cphnano/spincoater/spinner_hardware/Parts/SOLW_20170704_coupling.SLDPRT

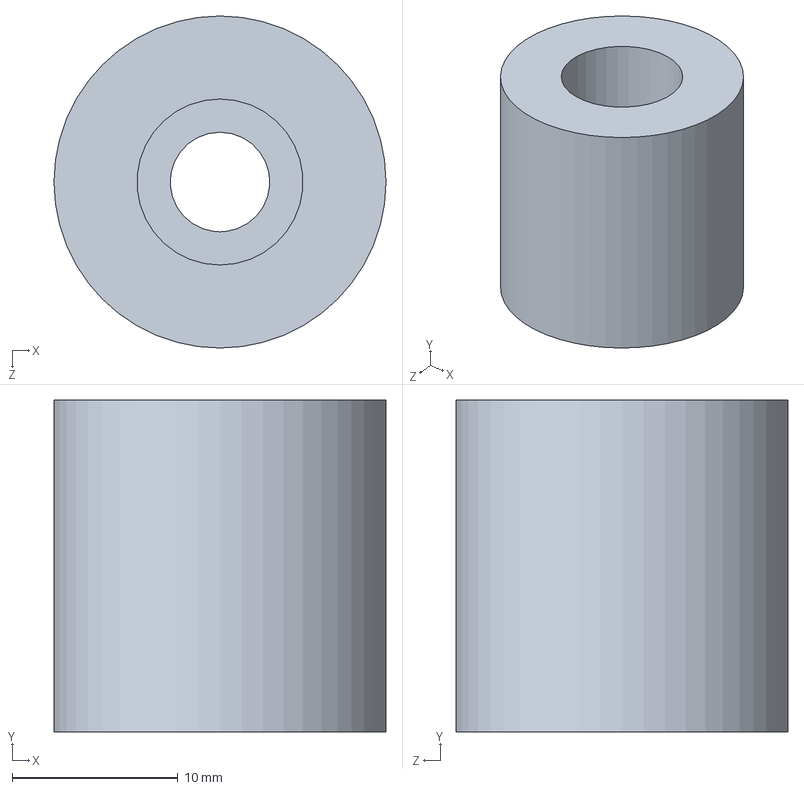
[picture p16: CAD file, 2019-01-21]
spinner_hardware/Parts/SOLW_20170704_coupling.SLDPRT
20.0 x 20.0 x 20.0 mm
