cphnano/spincoater/spinner_hardware/Parts/SOLW_20170703_Oring.SLDPRT

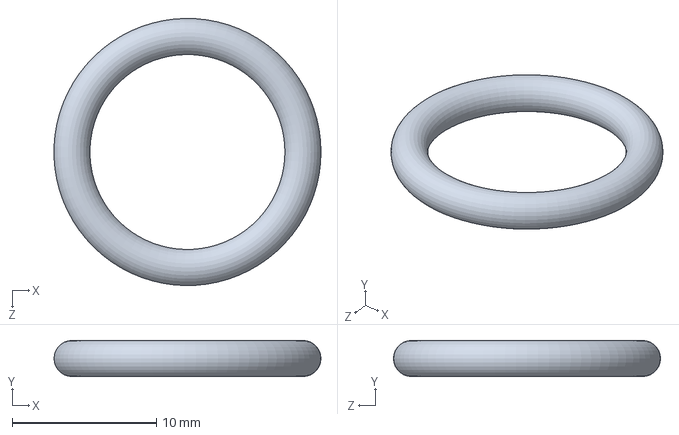
[picture p17: CAD file, 2019-01-21]
spinner_hardware/Parts/SOLW_20170703_Oring.SLDPRT
18.5 x 2.50 x 18.5 mm
