cphnano/spincoater/spinner_hardware/Parts/SOLW_20170707_JAw_Coupling_MJC25-10-A.SLDPRT

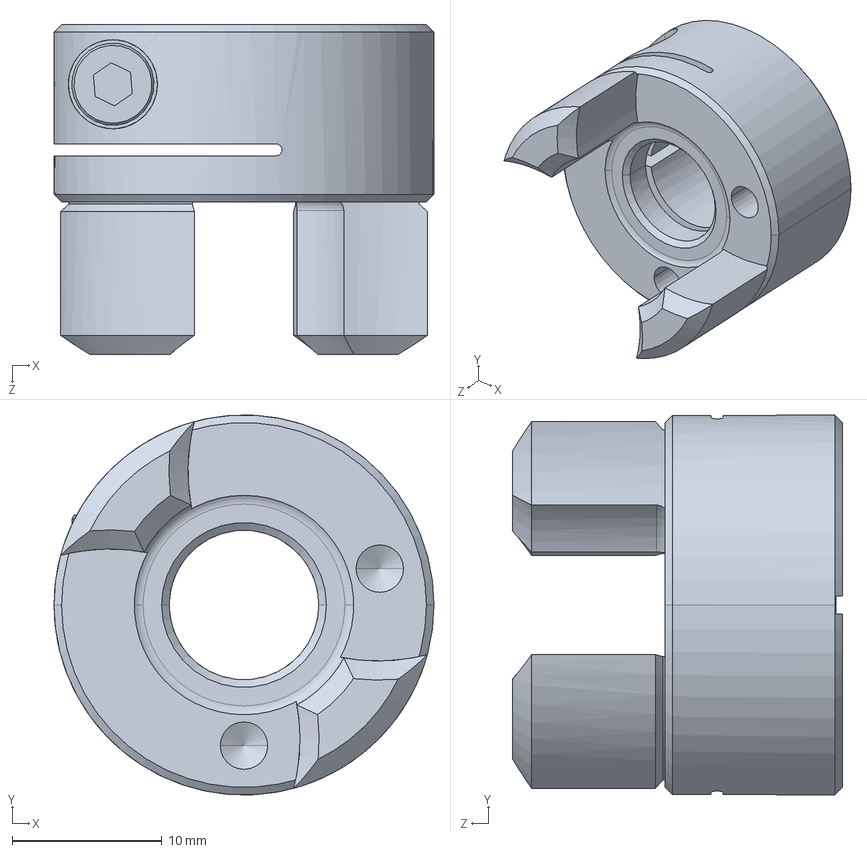
[picture p18: CAD file, 2019-01-21]
spinner_hardware/Parts/SOLW_20170707_JAw_Coupling_MJC25-10-A.SLDPRT
25.4 x 25.4 x 22.0 mm
