cphnano/spincoater/spinner_hardware/Parts/SOLW_20170703_static_clamp.SLDPRT

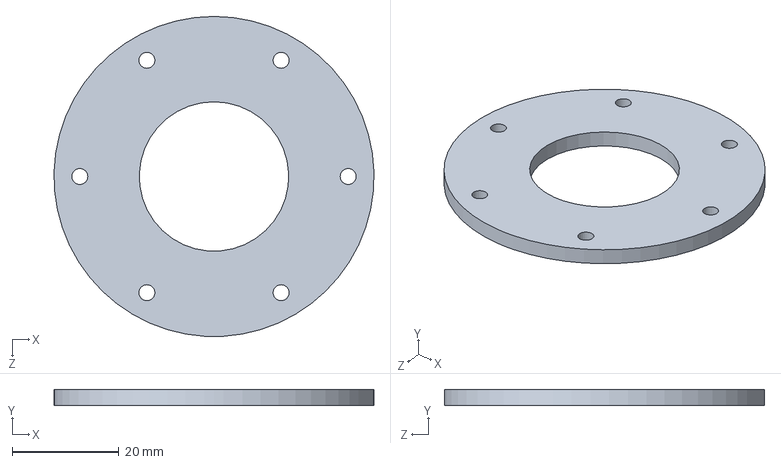
[picture p19: CAD file, 2019-01-21]
spinner_hardware/Parts/SOLW_20170703_static_clamp.SLDPRT
60.0 x 3.00 x 60.0 mm
