cphnano/spincoater/spinner_hardware/Parts/SOLW_20170724_Frequency_sensor.SLDPRT

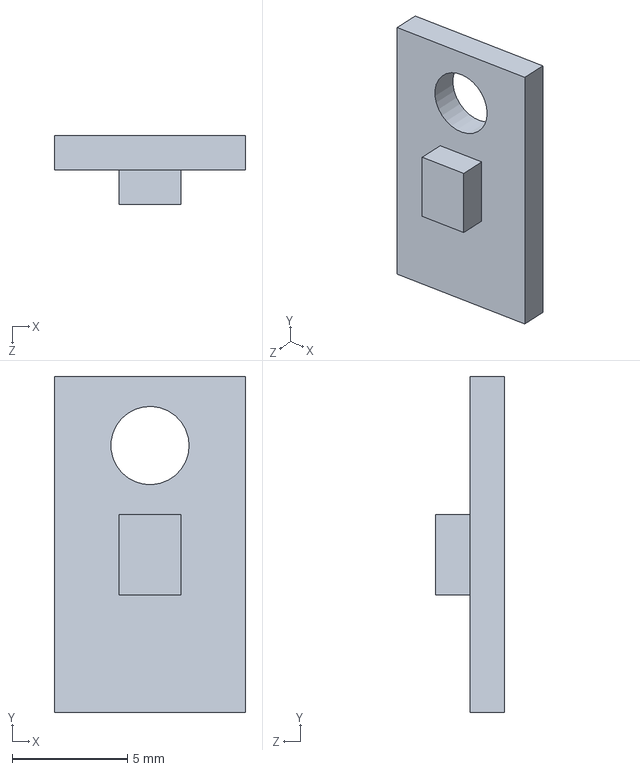
[picture p20: CAD file, 2019-01-21]
spinner_hardware/Parts/SOLW_20170724_Frequency_sensor.SLDPRT
8.30 x 14.6 x 3.00 mm
