cphnano/spincoater/spinner_hardware/Parts/SOLW_20170705_26.5X3_oring.SLDPRT

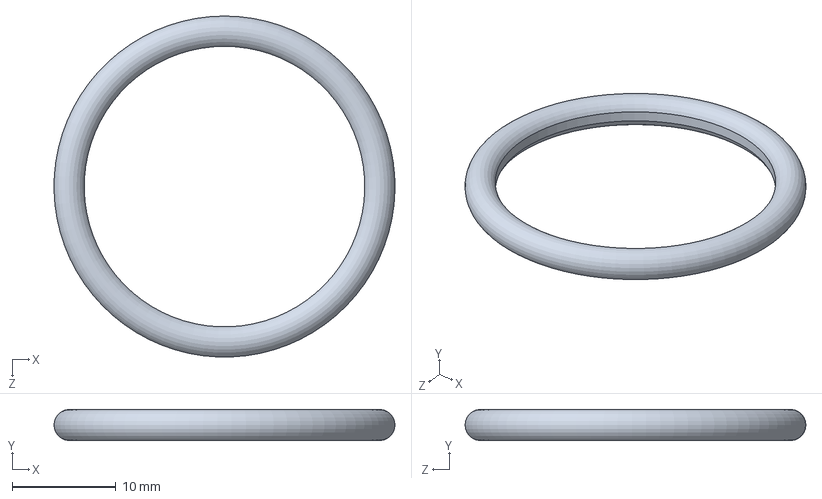
[picture p21: CAD file, 2019-01-21]
spinner_hardware/Parts/SOLW_20170705_26.5X3_oring.SLDPRT
32.8 x 3.00 x 32.8 mm
