cphnano/spincoater/spinner_hardware/Parts/SOLW_20170928_Aluminum Profile_3.SLDPRT

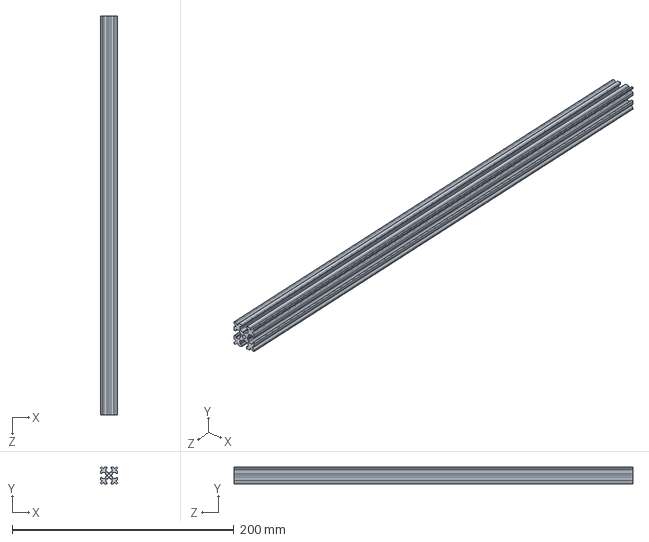
[picture p23: CAD file, 2019-01-21]
spinner_hardware/Parts/SOLW_20170928_Aluminum Profile_3.SLDPRT
15.0 x 15.0 x 360.0 mm
