cphnano/spincoater/spinner_hardware/Parts/SOLW_20170830_Bowl_side.SLDPRT

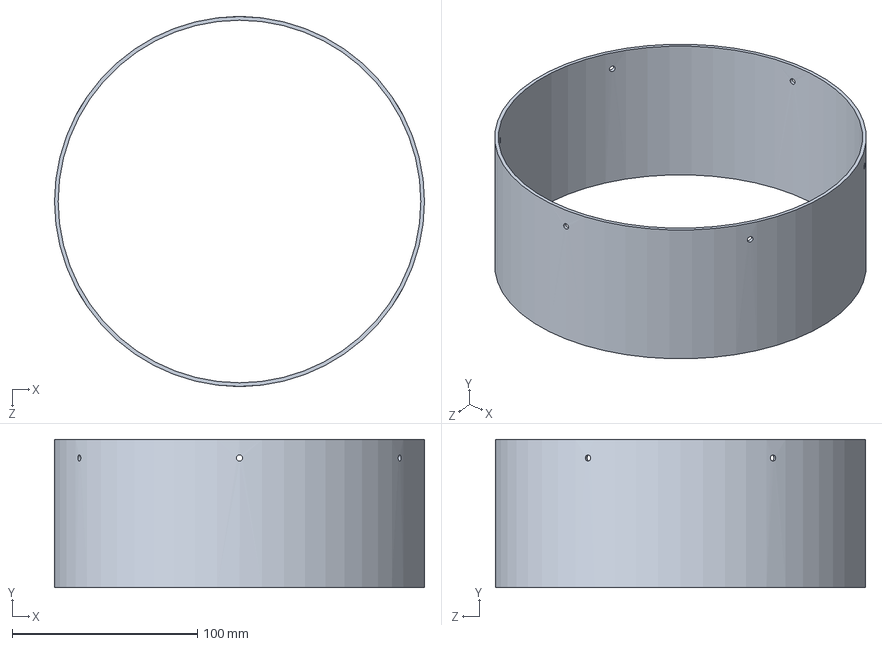
[picture p24: CAD file, 2019-01-21]
spinner_hardware/Parts/SOLW_20170830_Bowl_side.SLDPRT
200.0 x 80.0 x 200.0 mm
