cphnano/spincoater/spinner_hardware/Parts/SOLW_20170928_Aluminum Profile_2.SLDPRT

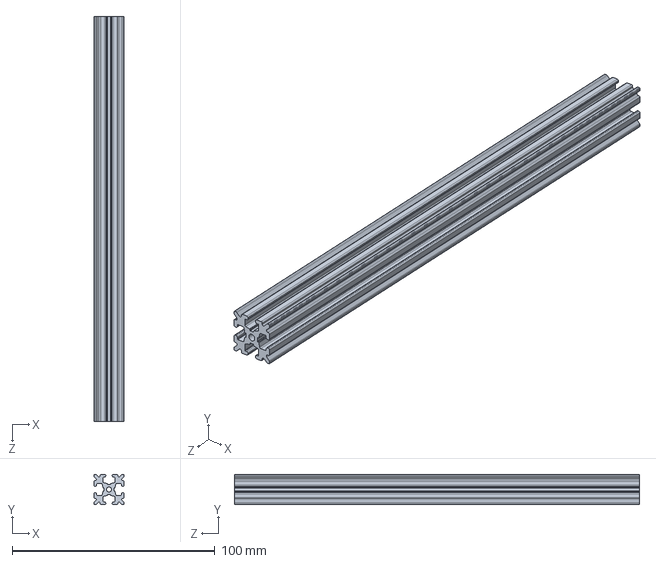
[picture p25: CAD file, 2019-01-21]
spinner_hardware/Parts/SOLW_20170928_Aluminum Profile_2.SLDPRT
15.0 x 15.0 x 200.0 mm
