cphnano/spincoater/spinner_hardware/Parts/SOLW_20170630_test_vacuum_chamber.SLDPRT

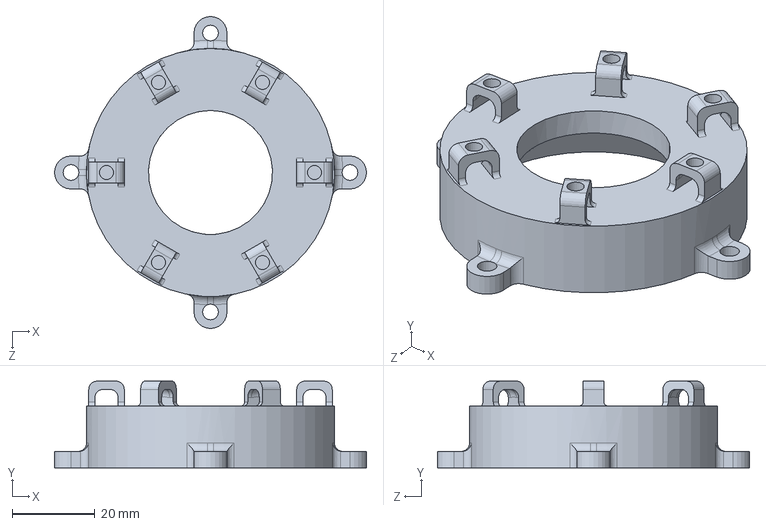
[picture p26: CAD file, 2019-01-21]
spinner_hardware/Parts/SOLW_20170630_test_vacuum_chamber.SLDPRT
75.5 x 21.0 x 75.5 mm
