cphnano/spincoater/spinner_hardware/Parts/SOLW_20170703_9.25X1.78Oring.SLDPRT

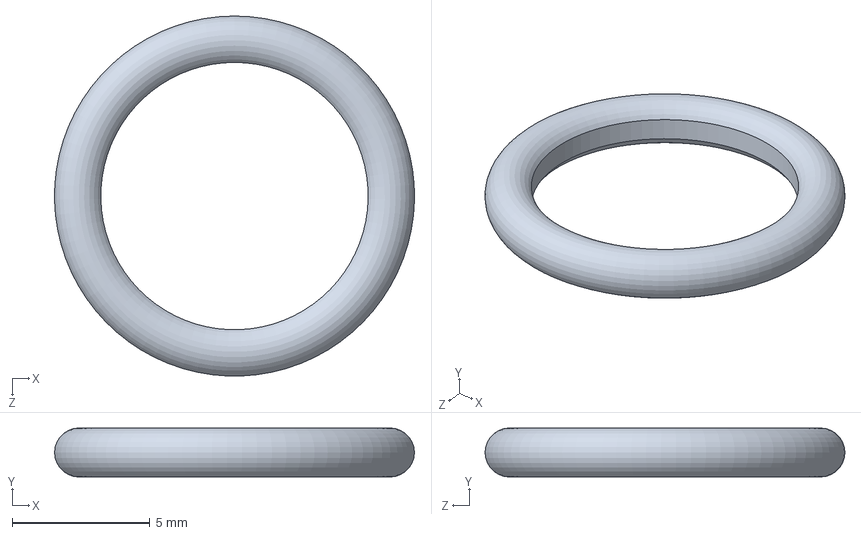
[picture p27: CAD file, 2019-01-21]
spinner_hardware/Parts/SOLW_20170703_9.25X1.78Oring.SLDPRT
13.1 x 1.78 x 13.1 mm
