cphnano/spincoater/spinner_hardware/Parts/SOLW_20170928_ArduinoMega2560.SLDPRT

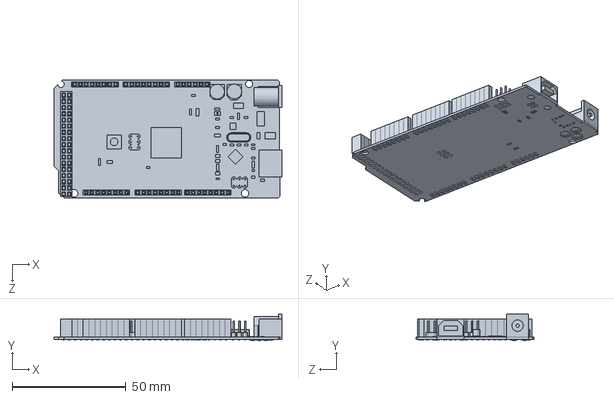
[picture p28: CAD file, 2019-01-21]
spinner_hardware/Parts/SOLW_20170928_ArduinoMega2560.SLDPRT
100.0 x 11.6 x 51.6 mm
