cphnano/spincoater/spinner_hardware/Parts/SOLW_20180612_Sheet6.SLDPRT

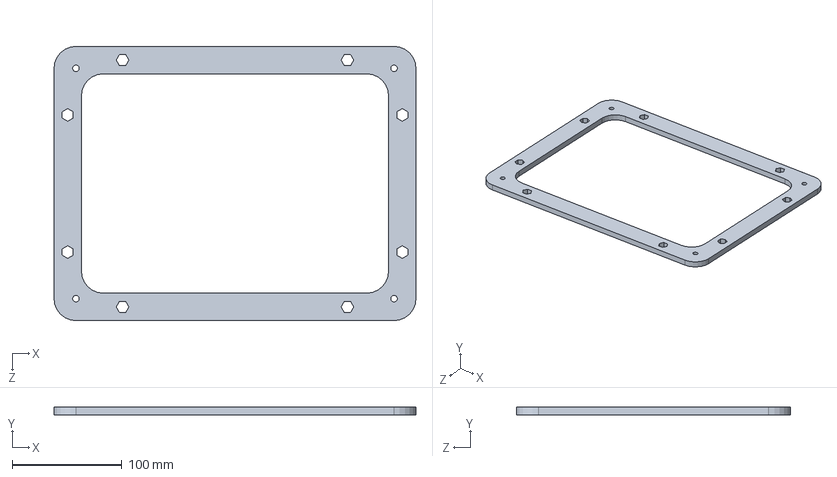
[picture p29: CAD file, 2019-01-21]
spinner_hardware/Parts/SOLW_20180612_Sheet6.SLDPRT
330.0 x 6.90 x 250.0 mm
