cphnano/spincoater/spinner_hardware/Parts/SOLW_20180613_legs.SLDPRT

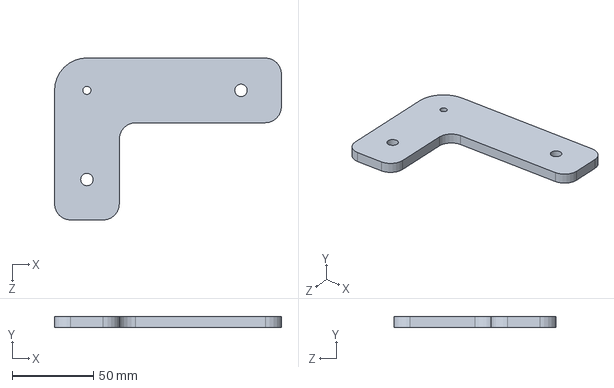
[picture p30: CAD file, 2019-01-21]
spinner_hardware/Parts/SOLW_20180613_legs.SLDPRT
140.0 x 6.90 x 100.0 mm
