cphnano/spincoater/spinner_hardware/Parts/SOLW_20170707_spider_JD16-25-92Y.SLDPRT

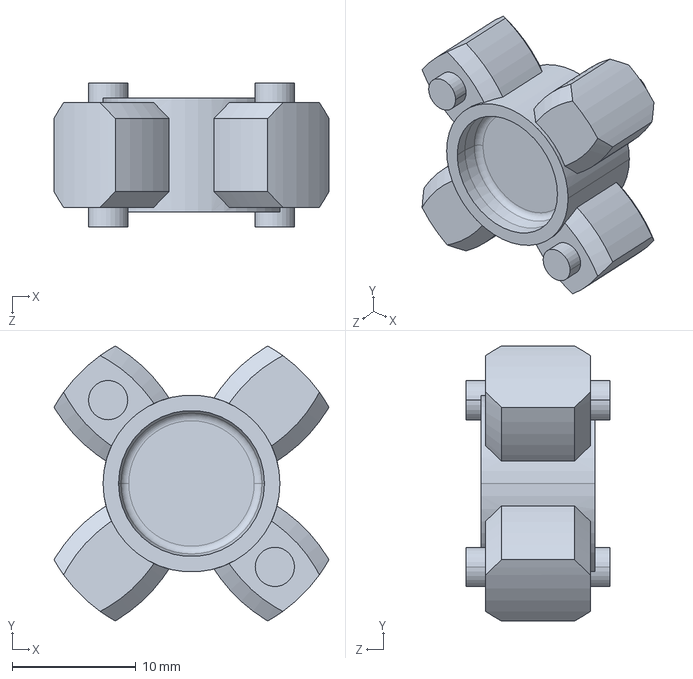
[picture p31: CAD file, 2019-01-21]
spinner_hardware/Parts/SOLW_20170707_spider_JD16-25-92Y.SLDPRT
22.2 x 22.2 x 11.6 mm
