cphnano/spincoater/spinner_hardware/Parts/SOLW_20170928_Aluminum Profile_5.SLDPRT

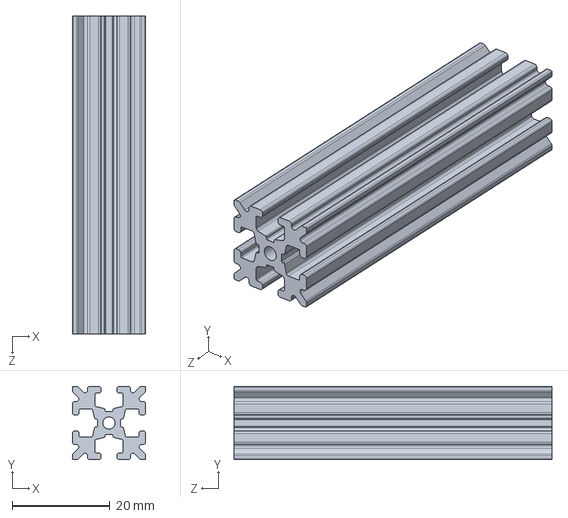
[picture p32: CAD file, 2019-01-21]
spinner_hardware/Parts/SOLW_20170928_Aluminum Profile_5.SLDPRT
15.0 x 15.0 x 65.0 mm
