cphnano/spincoater/spinner_hardware/Parts/SOLW_20170718_Cover.SLDPRT

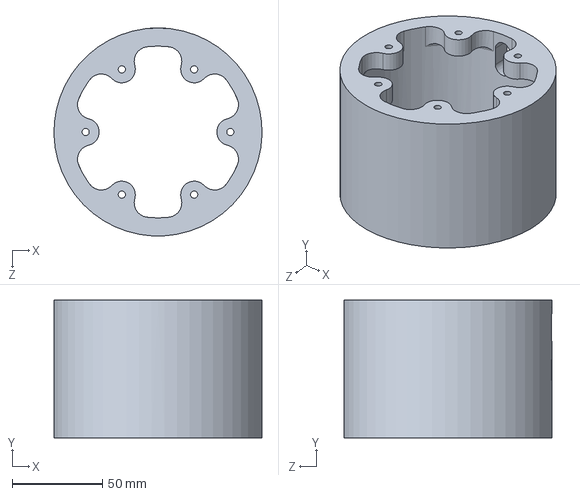
[picture p33: CAD file, 2019-01-21]
spinner_hardware/Parts/SOLW_20170718_Cover.SLDPRT
114.9 x 76.0 x 115.0 mm
