cphnano/spincoater/spinner_hardware/Parts/SOLW_20170929_PSU_Fixture4.SLDPRT

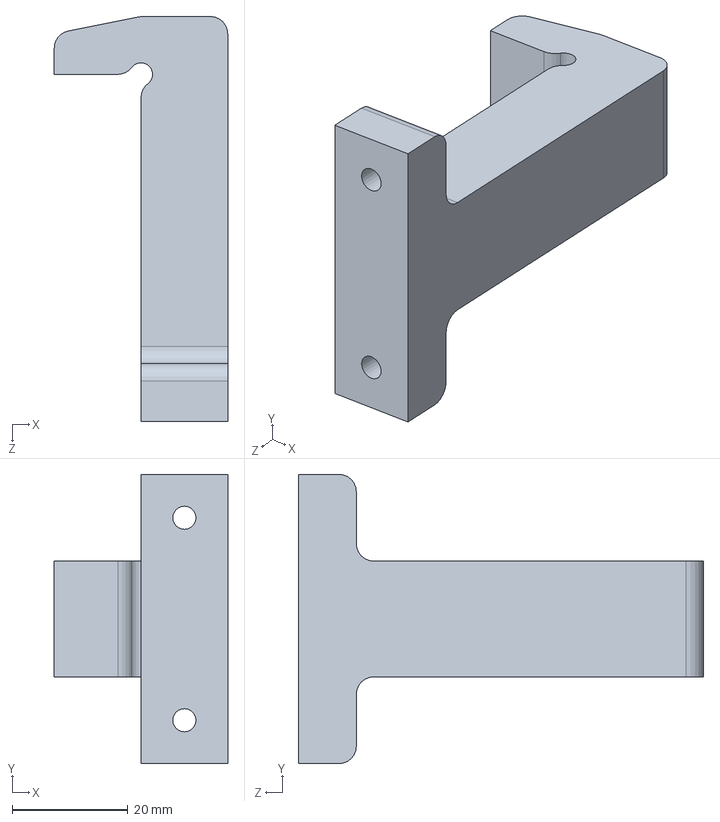
[picture p34: CAD file, 2019-01-21]
spinner_hardware/Parts/SOLW_20170929_PSU_Fixture4.SLDPRT
30.0 x 50.0 x 70.0 mm
