cphnano/spincoater/spinner_hardware/Parts/SOLW_20170704_vacuum_chamber_for_print.SLDPRT

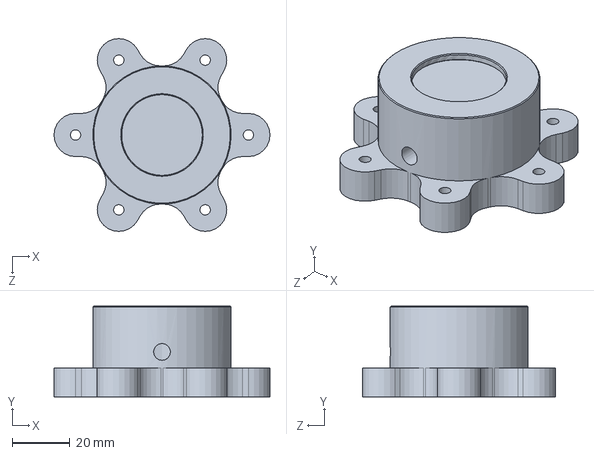
[picture p35: CAD file, 2019-01-21]
spinner_hardware/Parts/SOLW_20170704_vacuum_chamber_for_print.SLDPRT
75.0 x 31.5 x 67.0 mm
