cphnano/spincoater/spinner_hardware/Parts/SOLW_20180616_wafer_aligner_tool.SLDPRT

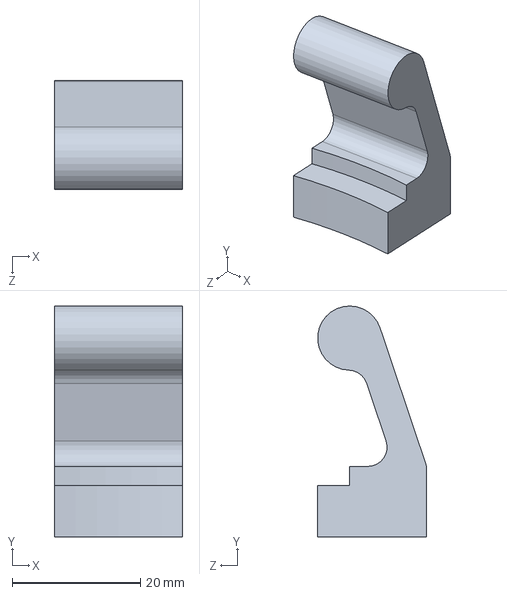
[picture p36: CAD file, 2019-01-21]
spinner_hardware/Parts/SOLW_20180616_wafer_aligner_tool.SLDPRT
20.0 x 36.0 x 17.0 mm
