cphnano/spincoater/spinner_hardware/Parts/SOLW_20170727_chuck.SLDPRT

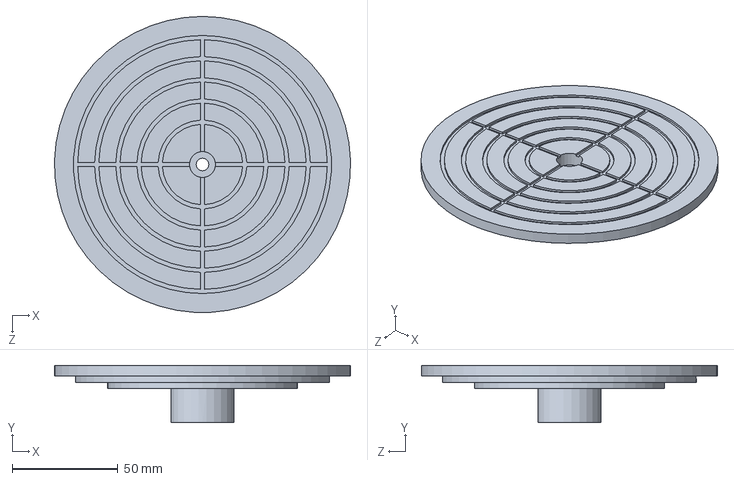
[picture p37: CAD file, 2019-01-21]
spinner_hardware/Parts/SOLW_20170727_chuck.SLDPRT
139.9 x 27.0 x 140.0 mm
