cphnano/spincoater/spinner_hardware/Parts/SOLW_20170720_stand.SLDPRT

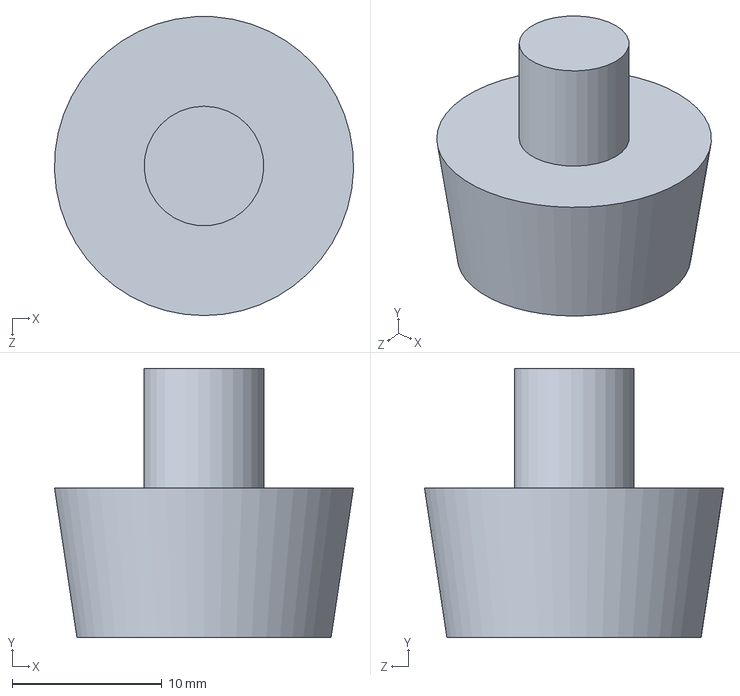
[picture p38: CAD file, 2019-01-21]
spinner_hardware/Parts/SOLW_20170720_stand.SLDPRT
20.0 x 18.0 x 20.0 mm
