cphnano/spincoater/spinner_hardware/Parts/SOLW_20170719_Bottom.SLDPRT

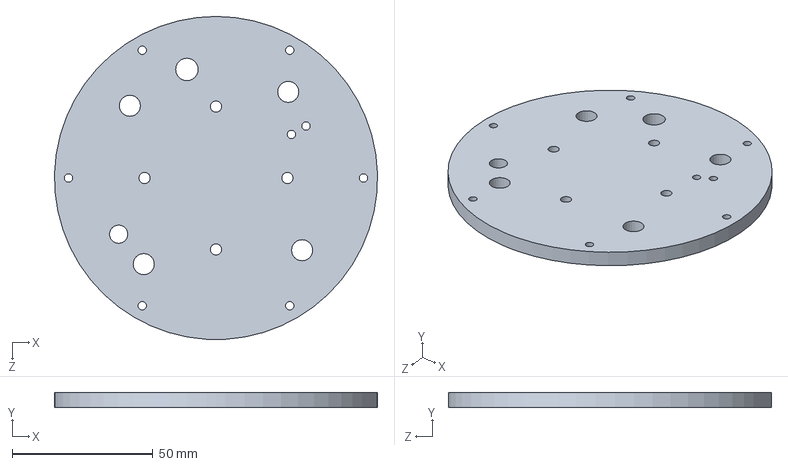
[picture p39: CAD file, 2019-01-21]
spinner_hardware/Parts/SOLW_20170719_Bottom.SLDPRT
114.9 x 5.50 x 115.0 mm
