cphnano/spincoater/spinner_hardware/Parts/SOLW_20170724_leg_of_Frequency_sensor.SLDPRT

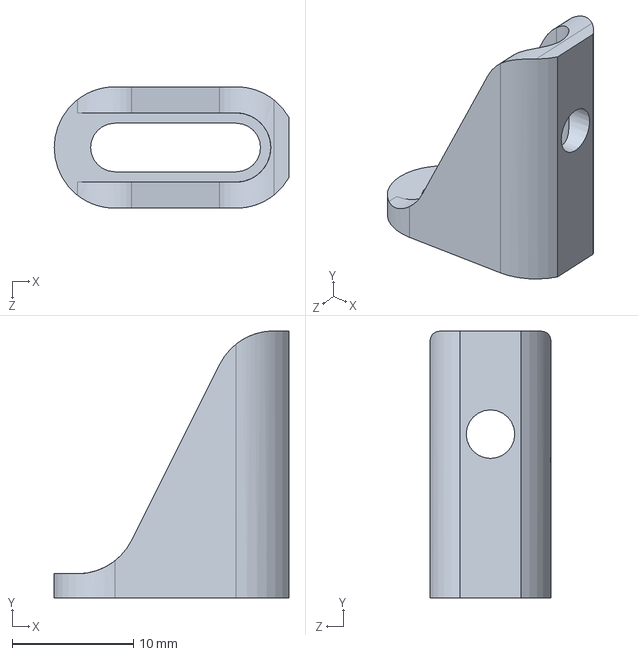
[picture p40: CAD file, 2019-01-21]
spinner_hardware/Parts/SOLW_20170724_leg_of_Frequency_sensor.SLDPRT
19.3 x 22.0 x 10.0 mm
