cphnano/spincoater/spinner_hardware/Parts/SOLW_20180612_DC_Brushless_Motor.SLDPRT

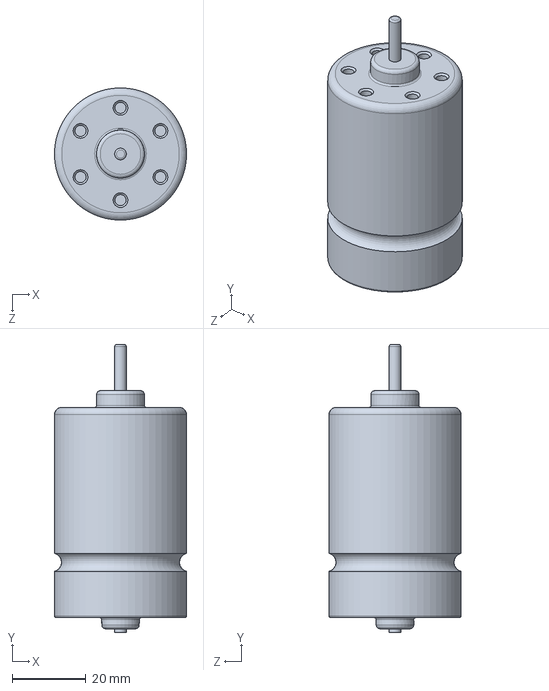
[picture p41: CAD file, 2019-01-21]
spinner_hardware/Parts/SOLW_20180612_DC_Brushless_Motor.SLDPRT
35.8 x 78.0 x 35.8 mm
