cphnano/spincoater/spinner_hardware/Parts/SOLW_20170706_Chamber.SLDPRT

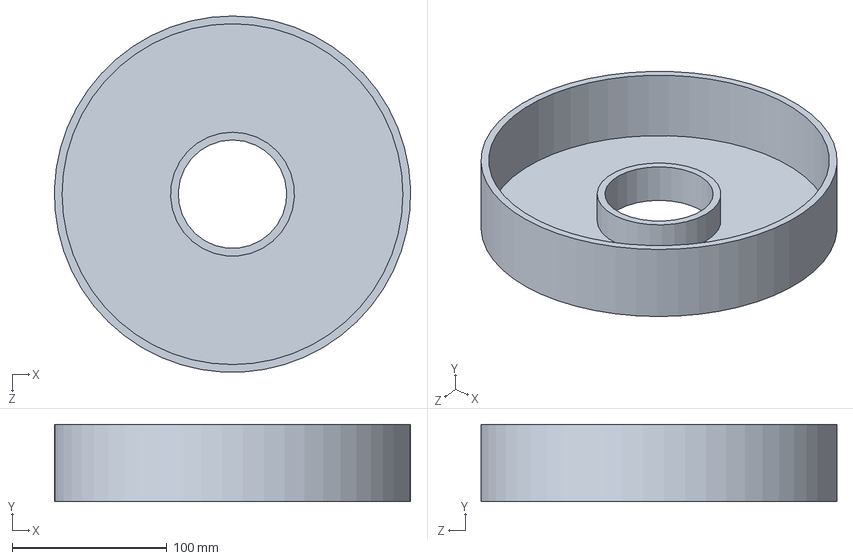
[picture p42: CAD file, 2019-01-21]
spinner_hardware/Parts/SOLW_20170706_Chamber.SLDPRT
229.9 x 50.0 x 229.8 mm
