cphnano/spincoater/spinner_hardware/Parts/SOLW_20170928_Aluminum Profile_1.SLDPRT

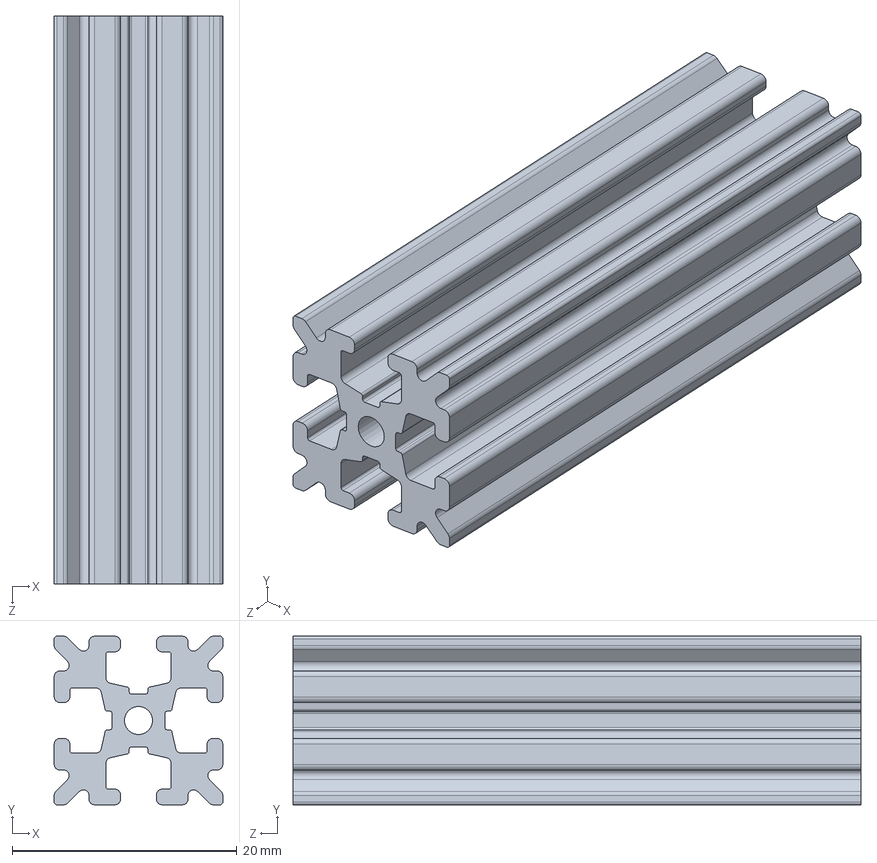
[picture p43: CAD file, 2019-01-21]
spinner_hardware/Parts/SOLW_20170928_Aluminum Profile_1.SLDPRT
15.0 x 15.0 x 50.5 mm
