cphnano/spincoater/spinner_hardware/Parts/SOLW_20170703_Bearing.SLDPRT

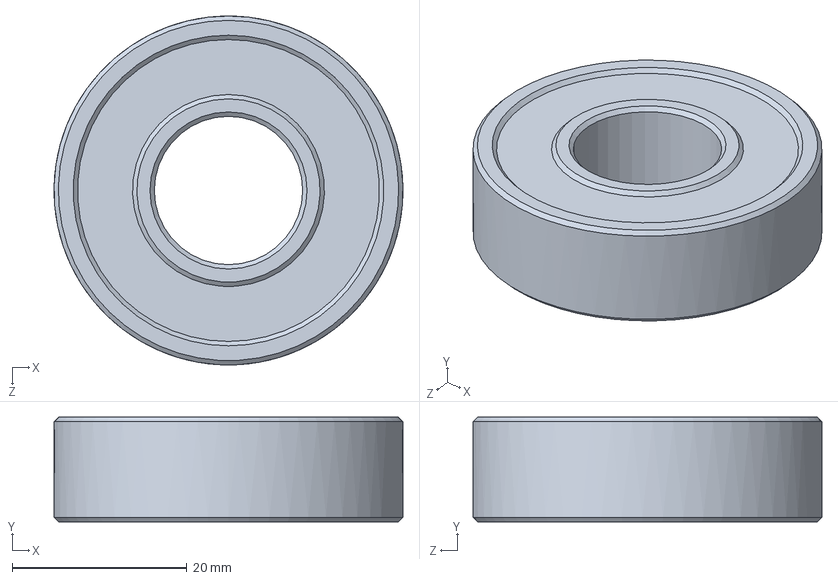
[picture p44: CAD file, 2019-01-21]
spinner_hardware/Parts/SOLW_20170703_Bearing.SLDPRT
40.0 x 12.0 x 40.0 mm
