cphnano/spincoater/spinner_hardware/Parts/SOLW_20170704_Cover_of_vacuum_chamber.SLDPRT

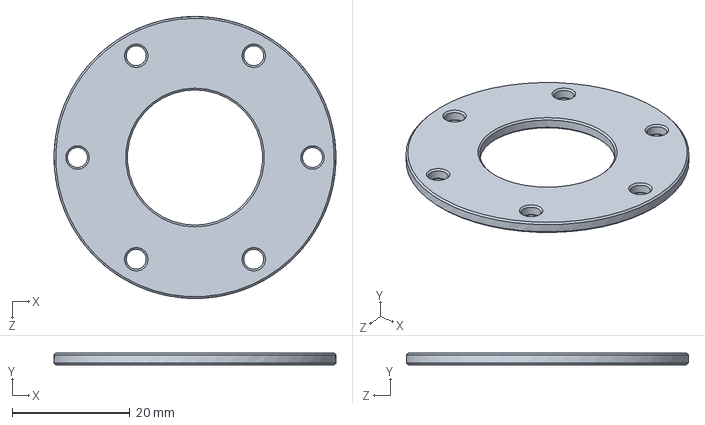
[picture p45: CAD file, 2019-01-21]
spinner_hardware/Parts/SOLW_20170704_Cover_of_vacuum_chamber.SLDPRT
48.0 x 2.00 x 48.0 mm
