cphnano/spincoater/spinner_hardware/Parts/SOLW_20170703_spinning_clamp_lock.SLDPRT

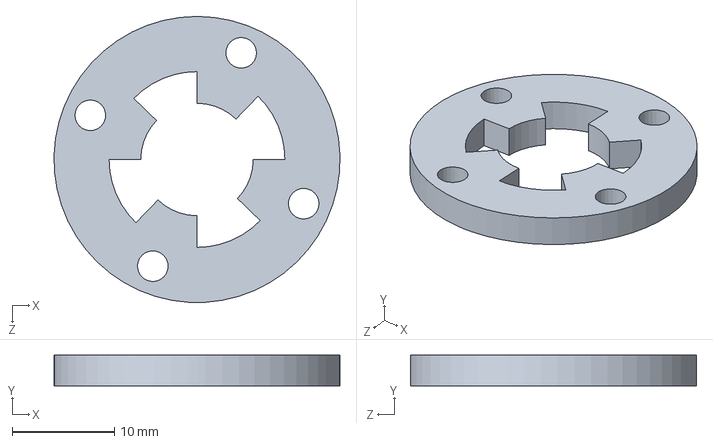
[picture p46: CAD file, 2019-01-21]
spinner_hardware/Parts/SOLW_20170703_spinning_clamp_lock.SLDPRT
28.0 x 3.00 x 28.0 mm
