cphnano/spincoater/spinner_hardware/Parts/SOLW_20170724_tube_holder.SLDPRT

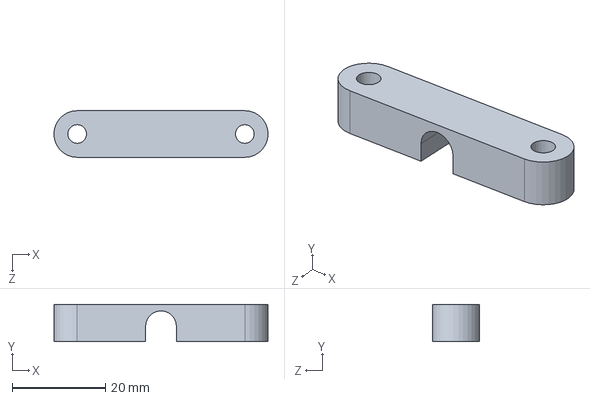
[picture p47: CAD file, 2019-01-21]
spinner_hardware/Parts/SOLW_20170724_tube_holder.SLDPRT
45.9 x 8.00 x 10.0 mm
