cphnano/spincoater/spinner_hardware/Parts/SOLW_20170616_Motor.SLDPRT

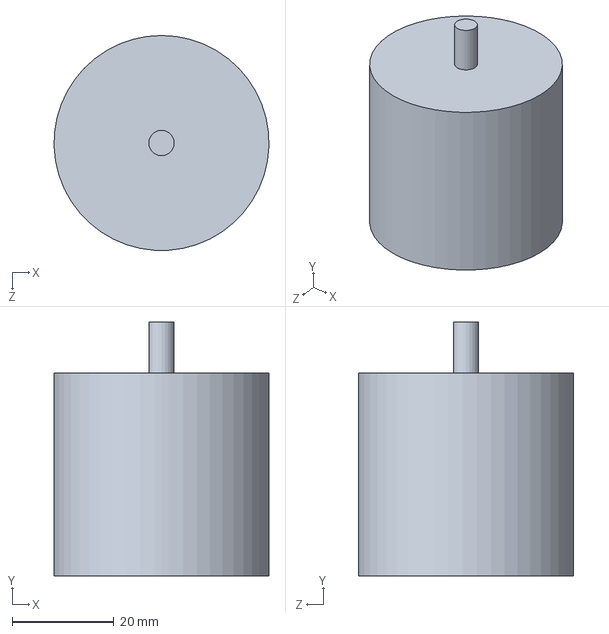
[picture p48: CAD file, 2019-01-21]
spinner_hardware/Parts/SOLW_20170616_Motor.SLDPRT
42.3 x 50.0 x 42.3 mm
