cphnano/spincoater/spinner_hardware/Parts/SOLW_20170929_PSU_Fixture2.SLDPRT

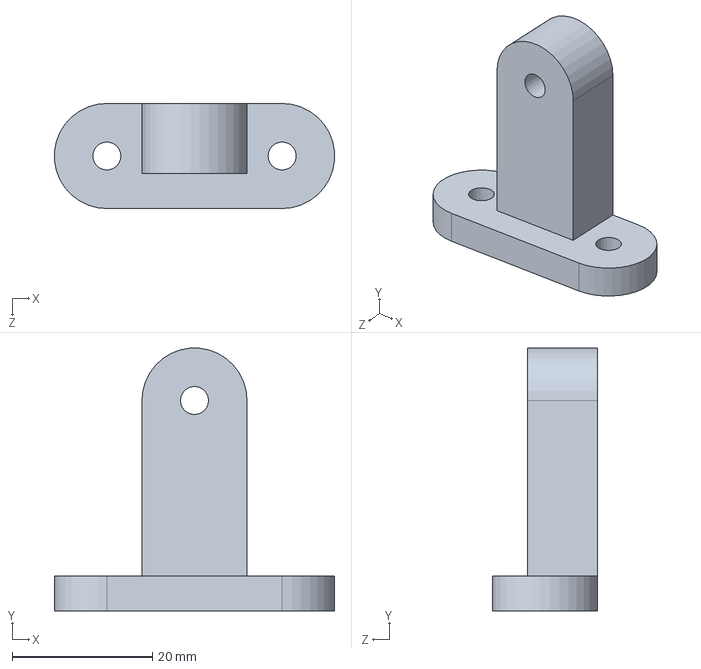
[picture p49: CAD file, 2019-01-21]
spinner_hardware/Parts/SOLW_20170929_PSU_Fixture2.SLDPRT
39.9 x 37.5 x 15.0 mm
