cphnano/spincoater/spinner_hardware/Parts/SOLW_20170704_12X28_Bearing.SLDPRT

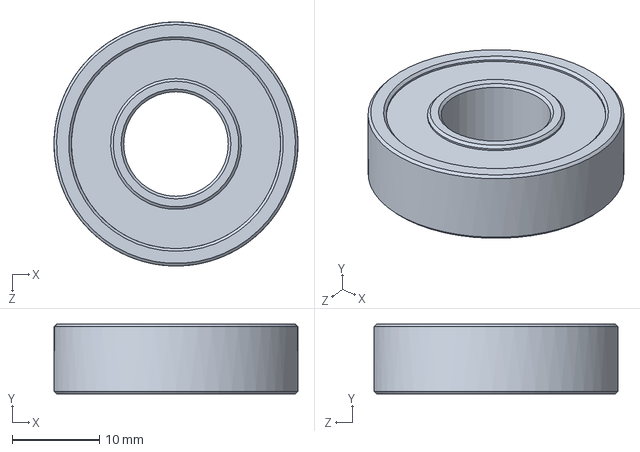
[picture p50: CAD file, 2019-01-21]
spinner_hardware/Parts/SOLW_20170704_12X28_Bearing.SLDPRT
28.0 x 8.00 x 28.0 mm
