cphnano/spincoater/spinner_hardware/Parts/SOLW_20170706_Base_plate.SLDPRT

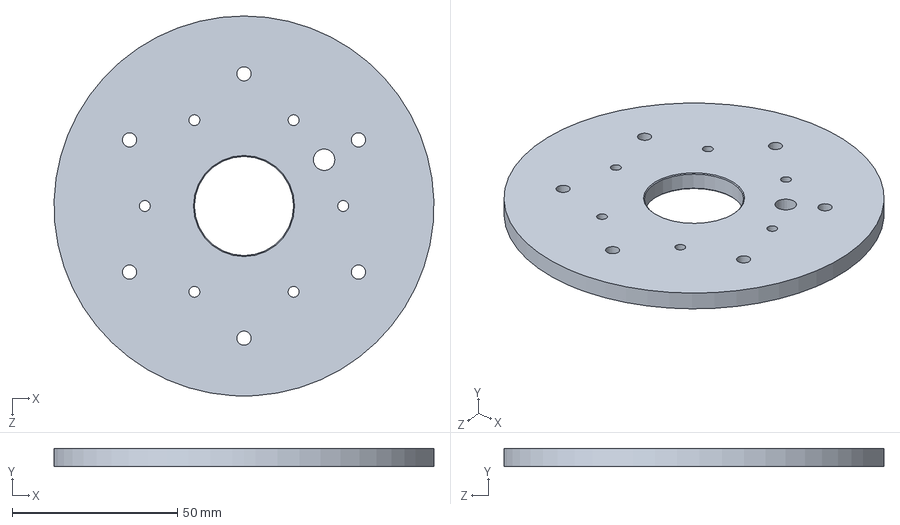
[picture p51: CAD file, 2019-01-21]
spinner_hardware/Parts/SOLW_20170706_Base_plate.SLDPRT
114.9 x 5.50 x 115.0 mm
