cphnano/spincoater/spinner_hardware/Parts/SOLW_20170703_Gasket.SLDPRT

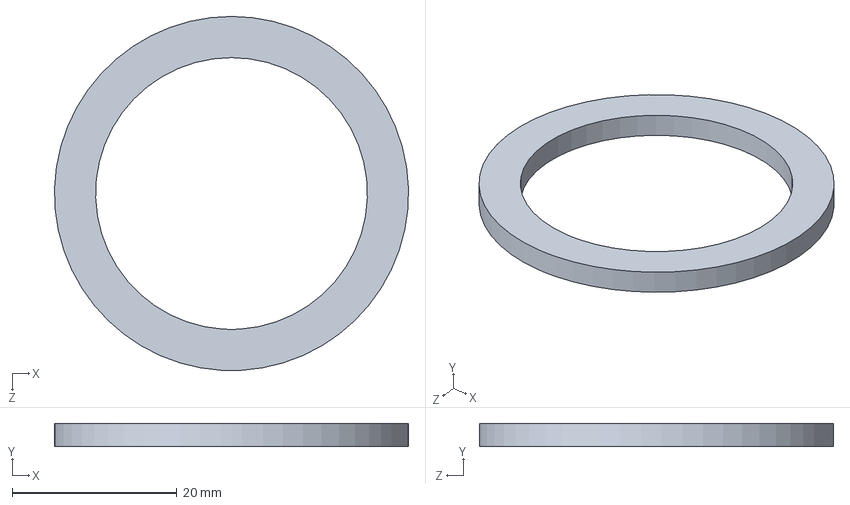
[picture p52: CAD file, 2019-01-21]
spinner_hardware/Parts/SOLW_20170703_Gasket.SLDPRT
43.0 x 2.80 x 43.0 mm
