cphnano/spincoater/spinner_hardware/Parts/SOLW_20170706_Pin.SLDPRT

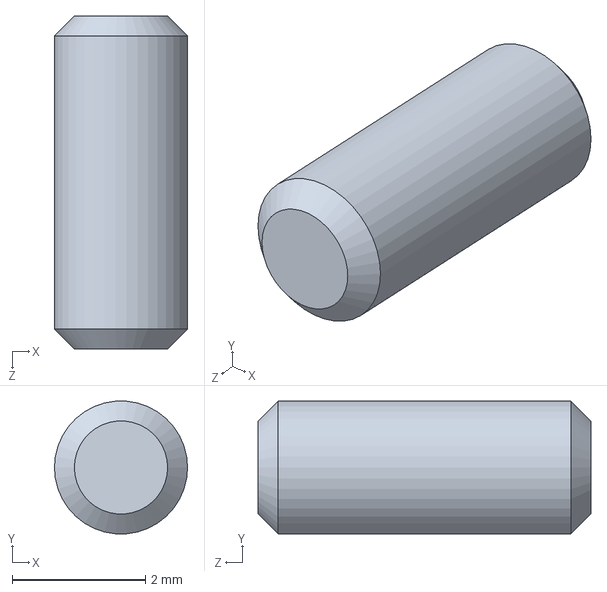
[picture p54: CAD file, 2019-01-21]
spinner_hardware/Parts/SOLW_20170706_Pin.SLDPRT
2.00 x 1.99 x 5.00 mm
