cphnano/spincoater/spinner_hardware/Parts/SOLW_20170704_double_bearing_Shaft_with_Oring_seat.SLDPRT

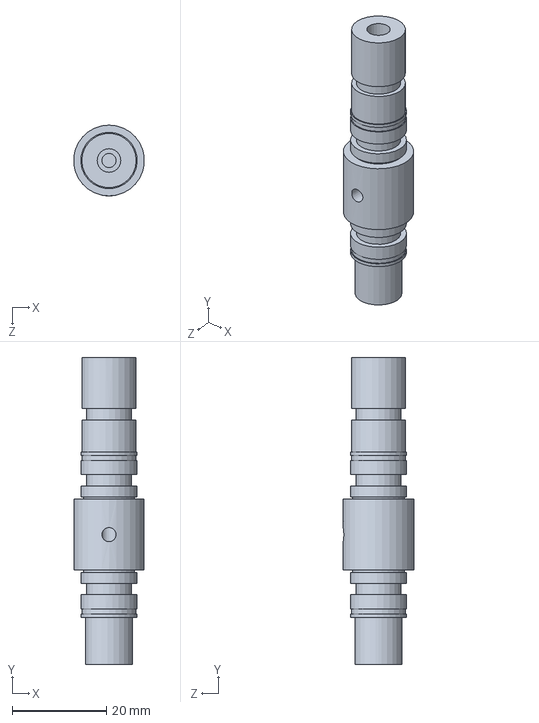
[picture p55: CAD file, 2019-01-21]
spinner_hardware/Parts/SOLW_20170704_double_bearing_Shaft_with_Oring_seat.SLDPRT
14.9 x 65.0 x 15.0 mm
