cphnano/spincoater/spinner_hardware/Parts/SOLW_20170830_Bowl_top_side_connector.SLDPRT

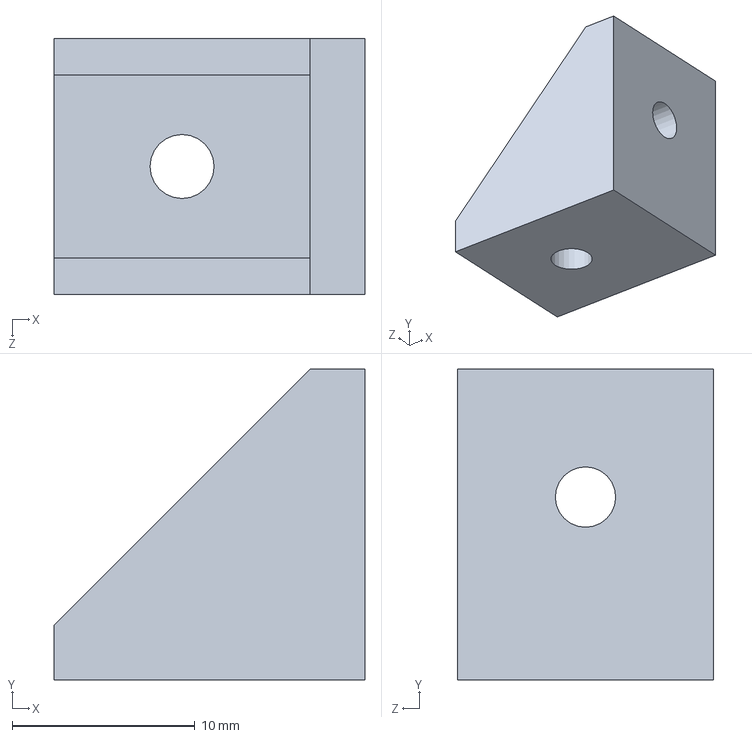
[picture p56: CAD file, 2019-01-21]
spinner_hardware/Parts/SOLW_20170830_Bowl_top_side_connector.SLDPRT
17.0 x 17.0 x 14.0 mm
