cphnano/spincoater/spinner_hardware/Parts/SOLW_20170620_chuck_dummy.SLDPRT

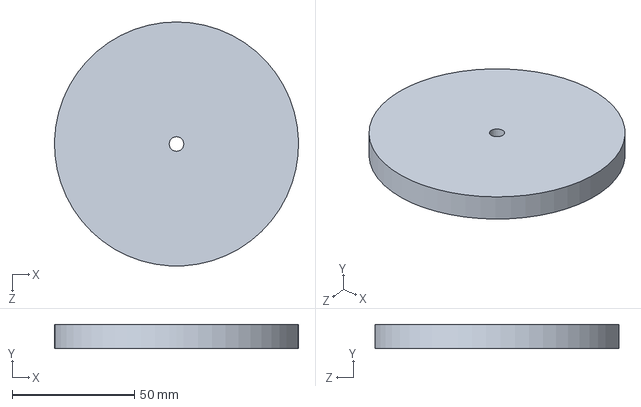
[picture p57: CAD file, 2019-01-21]
spinner_hardware/Parts/SOLW_20170620_chuck_dummy.SLDPRT
100.0 x 10.0 x 100.0 mm
