cphnano/spincoater/spinner_hardware/Parts/SOLW_20170704_vacuum_chamber.SLDPRT

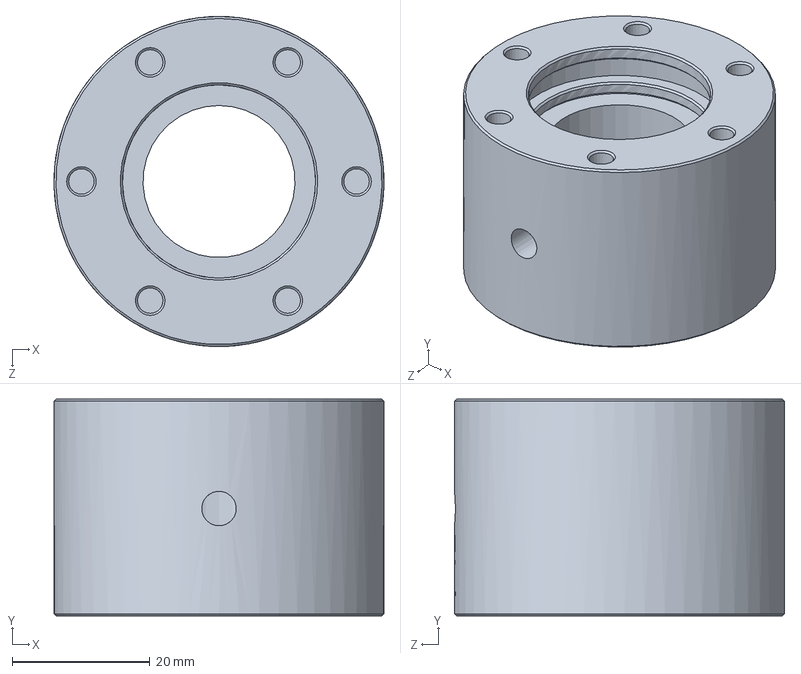
[picture p58: CAD file, 2019-01-21]
spinner_hardware/Parts/SOLW_20170704_vacuum_chamber.SLDPRT
48.0 x 31.5 x 48.0 mm
