cphnano/spincoater/spinner_hardware/Parts/SOLW_20170703_spinning_clamp_seat.SLDPRT

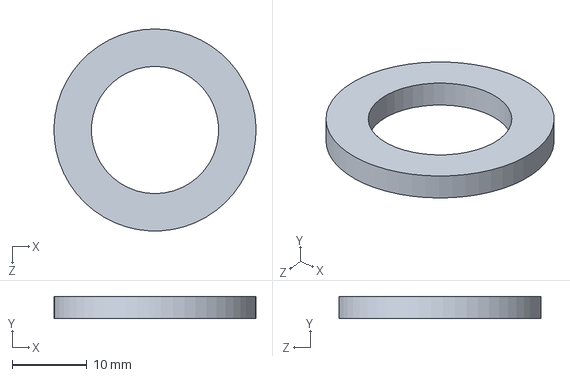
[picture p59: CAD file, 2019-01-21]
spinner_hardware/Parts/SOLW_20170703_spinning_clamp_seat.SLDPRT
27.0 x 3.00 x 27.0 mm
