cphnano/spincoater/spinner_hardware/Parts/SOLW_20170703_17.17X1.78Oring.SLDPRT

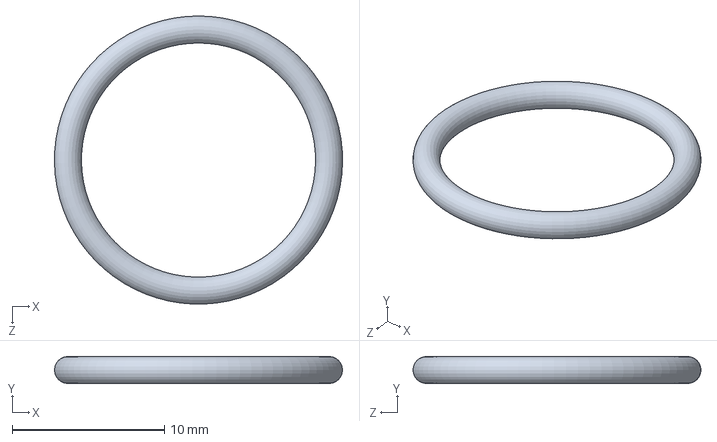
[picture p60: CAD file, 2019-01-21]
spinner_hardware/Parts/SOLW_20170703_17.17X1.78Oring.SLDPRT
18.9 x 1.78 x 18.9 mm
