cphnano/spincoater/spinner_hardware/Parts/SOLW_20170719_Chamber.SLDPRT

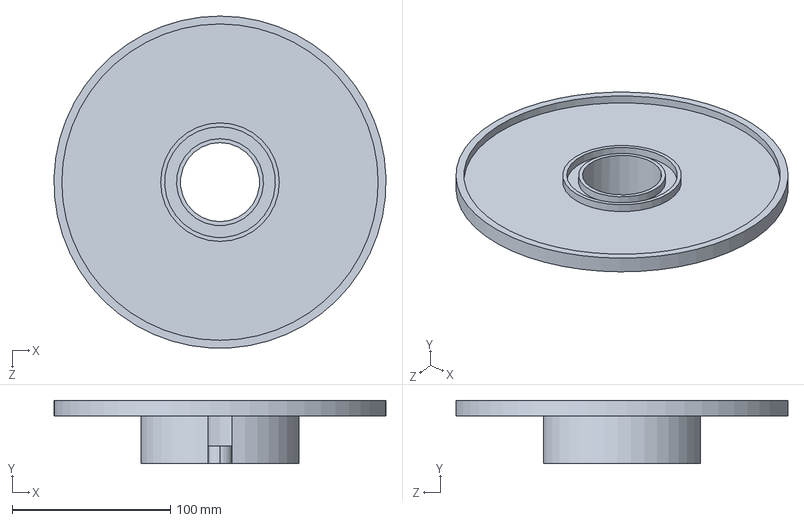
[picture p61: CAD file, 2019-01-21]
spinner_hardware/Parts/SOLW_20170719_Chamber.SLDPRT
209.9 x 40.0 x 209.8 mm
