cphnano/spincoater/spinner_hardware/Parts/SOLW_20170517_Chamber_inclined.SLDPRT

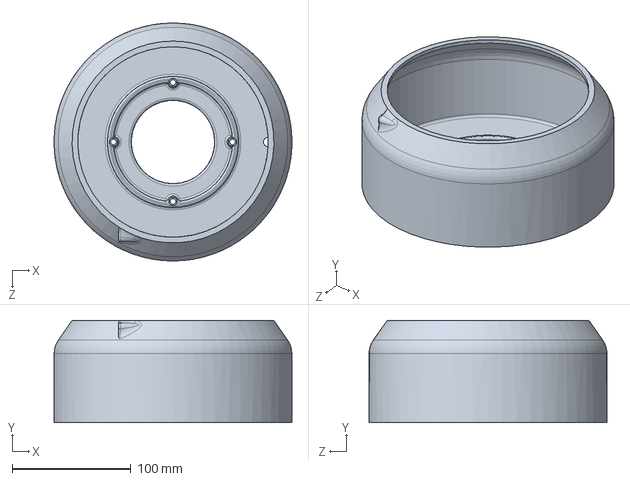
[picture p62: CAD file, 2019-01-21]
spinner_hardware/Parts/SOLW_20170517_Chamber_inclined.SLDPRT
200.0 x 86.0 x 200.0 mm
