cphnano/spincoater/spinner_hardware/Parts/SOLW_20170927_Power_Supply.SLDPRT

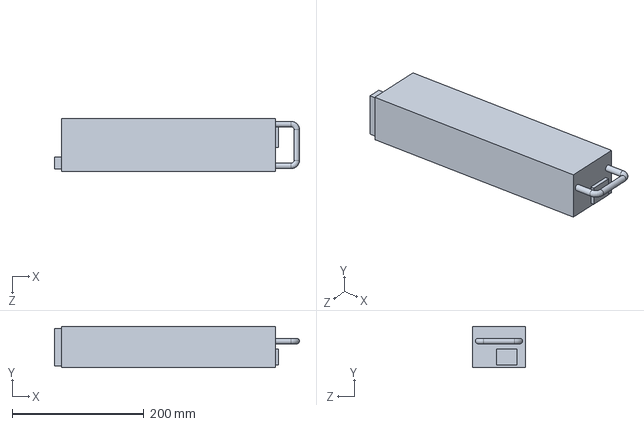
[picture p63: CAD file, 2019-01-21]
spinner_hardware/Parts/SOLW_20170927_Power_Supply.SLDPRT
372.2 x 63.0 x 80.0 mm
